mostafa-khalid208/SMART-TECHNOLOGY-APPLICATIONS-IN-AGRICULTURE/APK & Code/smart_irrigation/smart_irrigation/assets/images/8i88iu.jpg

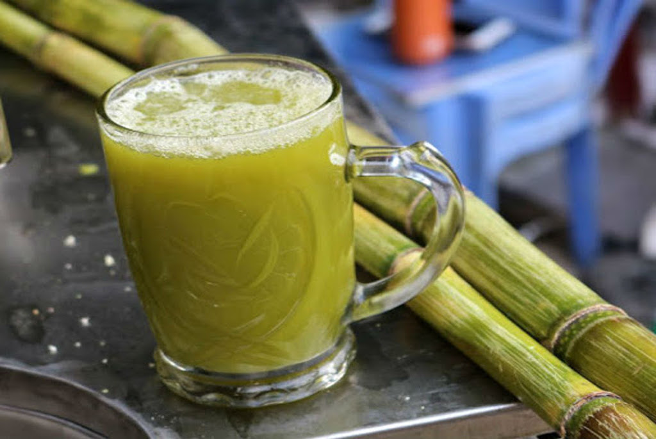
APK & Code/smart_irrigation/smart_irrigation/assets/images/8i88iu.jpg
