mostafa-khalid208/SMART-TECHNOLOGY-APPLICATIONS-IN-AGRICULTURE/APK & Code/smart_irrigation/smart_irrigation/assets/images/2021-10-02.jpg

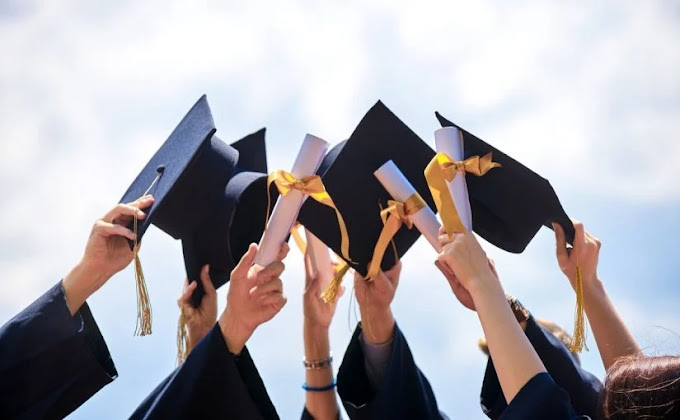
APK & Code/smart_irrigation/smart_irrigation/assets/images/2021-10-02.jpg
