mostafa-khalid208/SMART-TECHNOLOGY-APPLICATIONS-IN-AGRICULTURE/APK & Code/smart_irrigation/smart_irrigation/assets/images/download.jpg

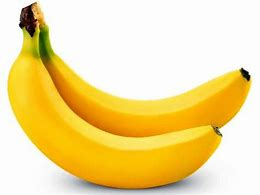
APK & Code/smart_irrigation/smart_irrigation/assets/images/download.jpg
