mostafa-khalid208/SMART-TECHNOLOGY-APPLICATIONS-IN-AGRICULTURE/APK & Code/smart_irrigation/smart_irrigation/assets/images/grg.jpg

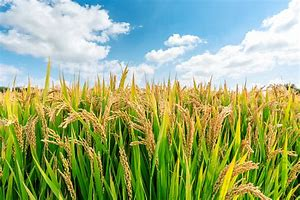
APK & Code/smart_irrigation/smart_irrigation/assets/images/grg.jpg
