mostafa-khalid208/SMART-TECHNOLOGY-APPLICATIONS-IN-AGRICULTURE/Diagram (Fritzing)/Diagram_png.png

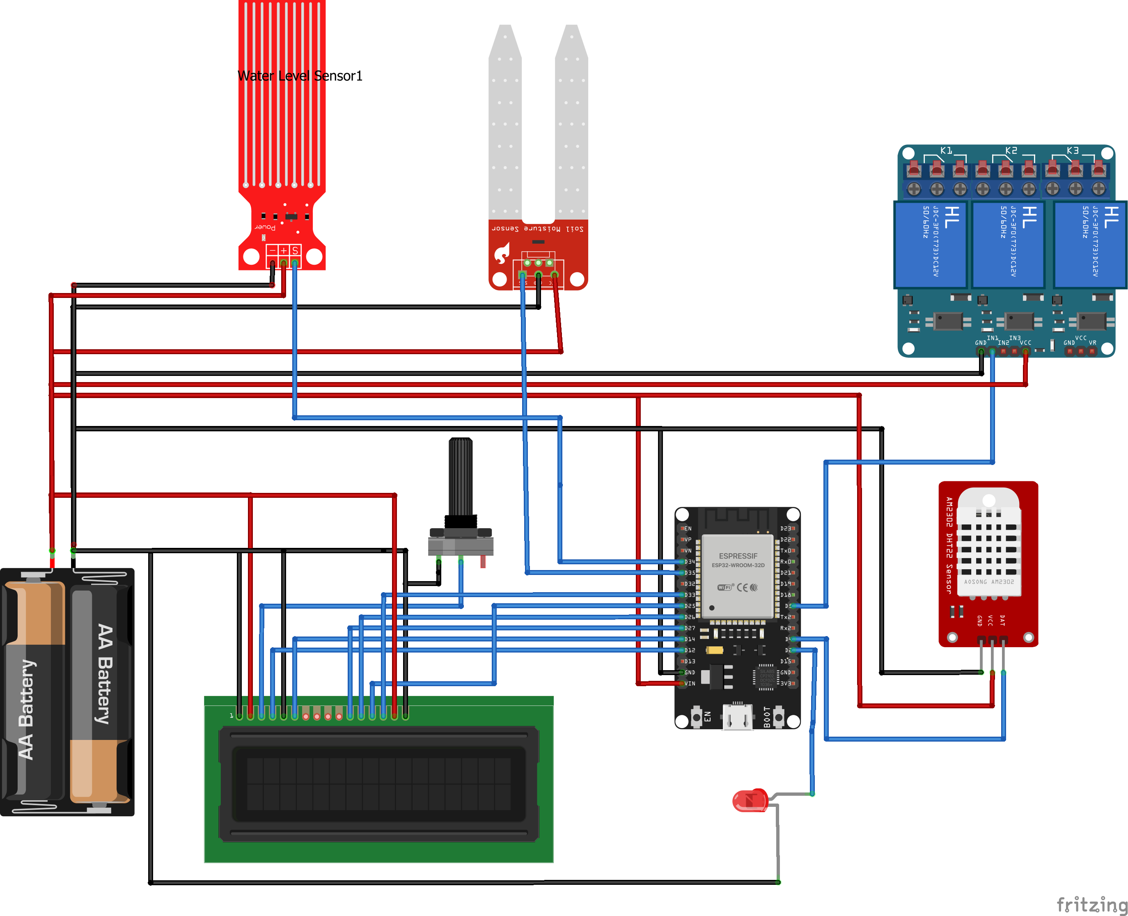
Diagram (Fritzing)/Diagram_png.png
