mostafa-khalid208/SMART-TECHNOLOGY-APPLICATIONS-IN-AGRICULTURE/KiCAD_ESP32/PCB.png

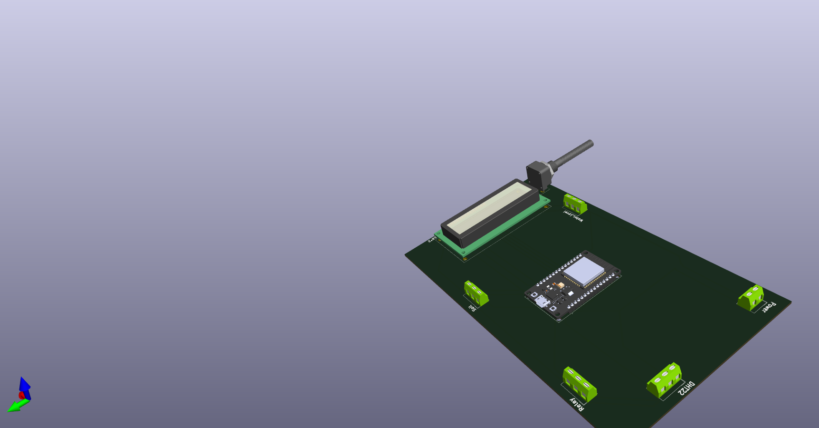
KiCAD_ESP32/PCB.png
