mostafa-khalid208/SMART-TECHNOLOGY-APPLICATIONS-IN-AGRICULTURE/KiCAD_ESP32/PCB_3.jpg

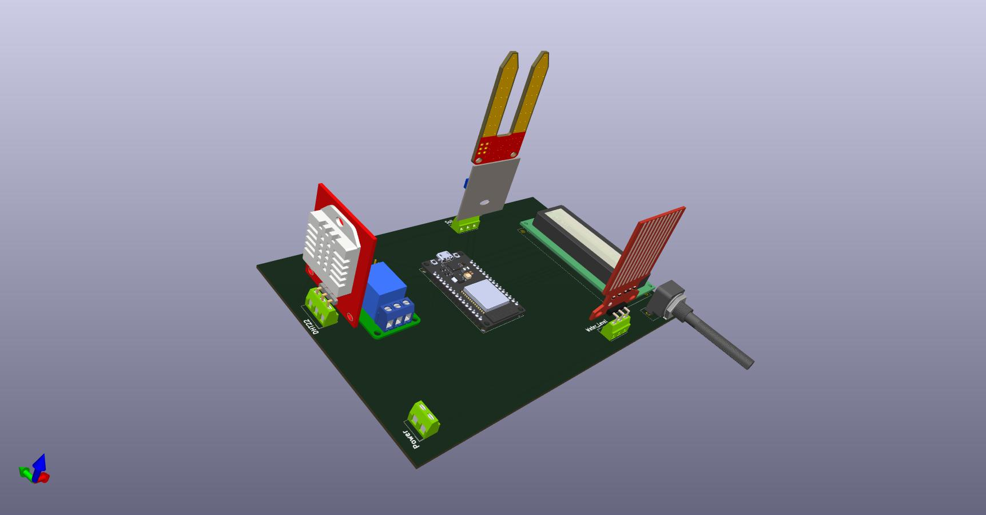
KiCAD_ESP32/PCB_3.jpg
