mostafa-khalid208/SMART-TECHNOLOGY-APPLICATIONS-IN-AGRICULTURE/QRs/All graduation project files (Google Drive).jpg

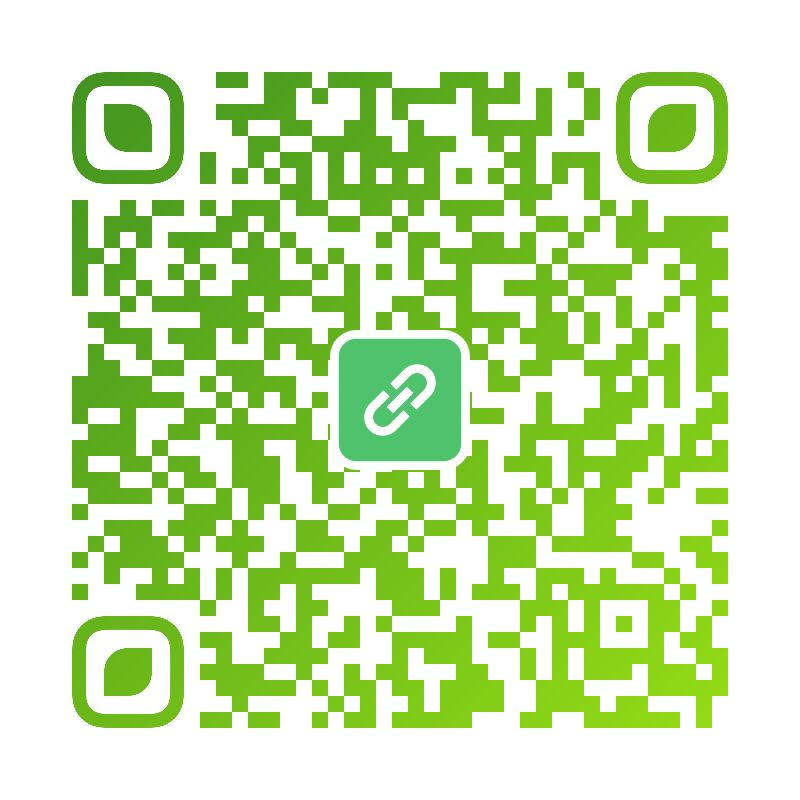
QRs/All graduation project files (Google Drive).jpg
