mostafa-khalid208/SMART-TECHNOLOGY-APPLICATIONS-IN-AGRICULTURE/QRs/Final practical application of the graduation project.jpg

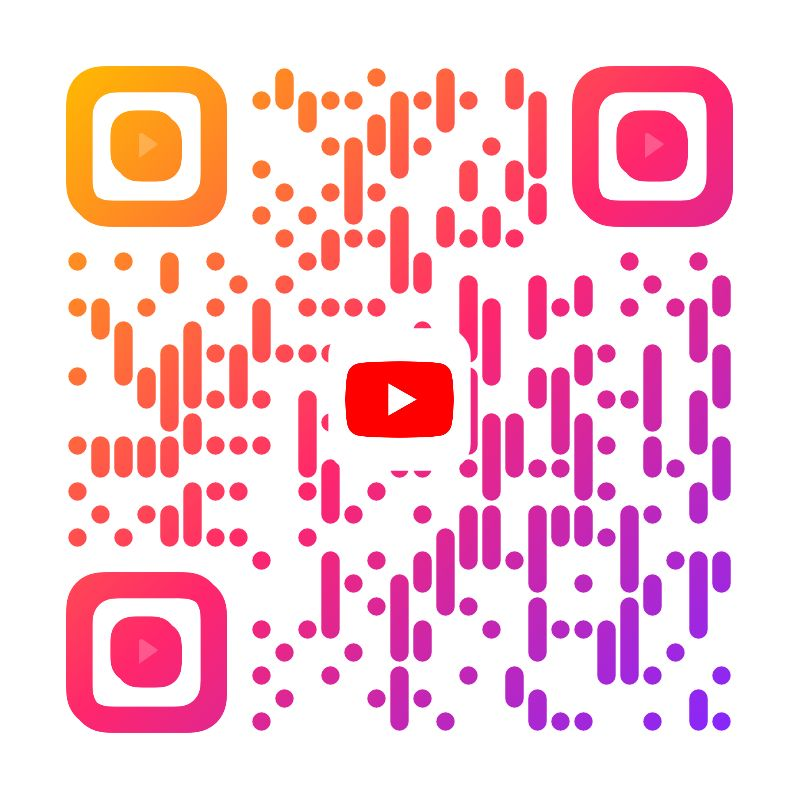
QRs/Final practical application of the graduation project.jpg
