mostafa-khalid208/SMART-TECHNOLOGY-APPLICATIONS-IN-AGRICULTURE/QRs/Github_Link_QR.png

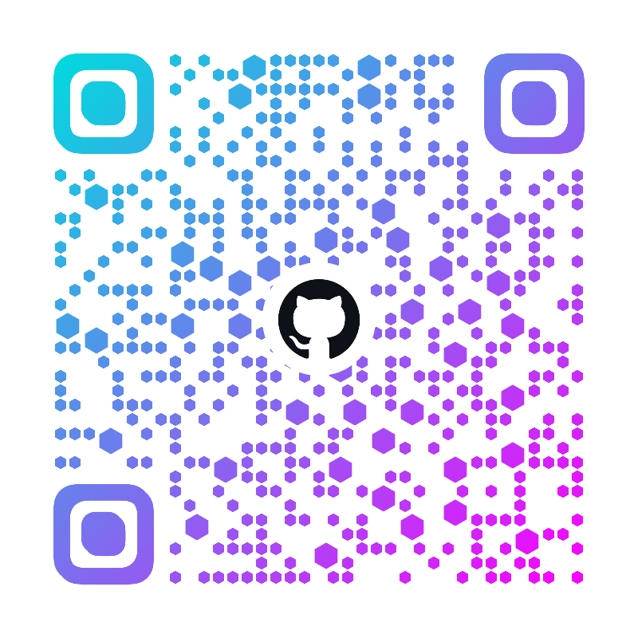
QRs/Github_Link_QR.png
