mostafa-khalid208/SMART-TECHNOLOGY-APPLICATIONS-IN-AGRICULTURE/QRs/Graduation project students with project supervisor.jpg

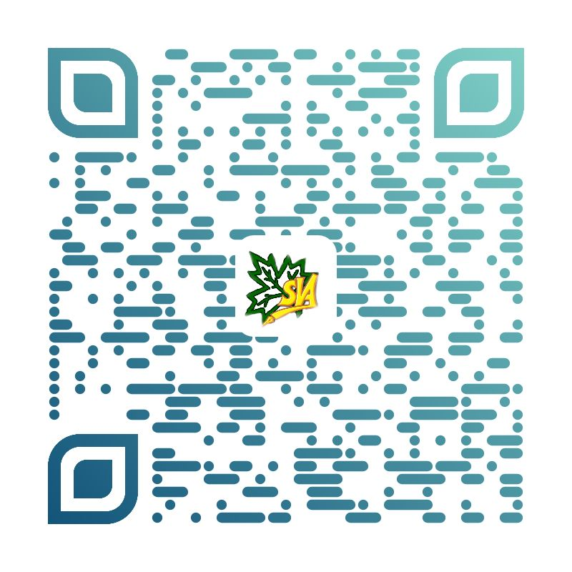
QRs/Graduation project students with project supervisor.jpg
