mostafa-khalid208/SMART-TECHNOLOGY-APPLICATIONS-IN-AGRICULTURE/QRs/Playlist on YouTube has all the videos.png

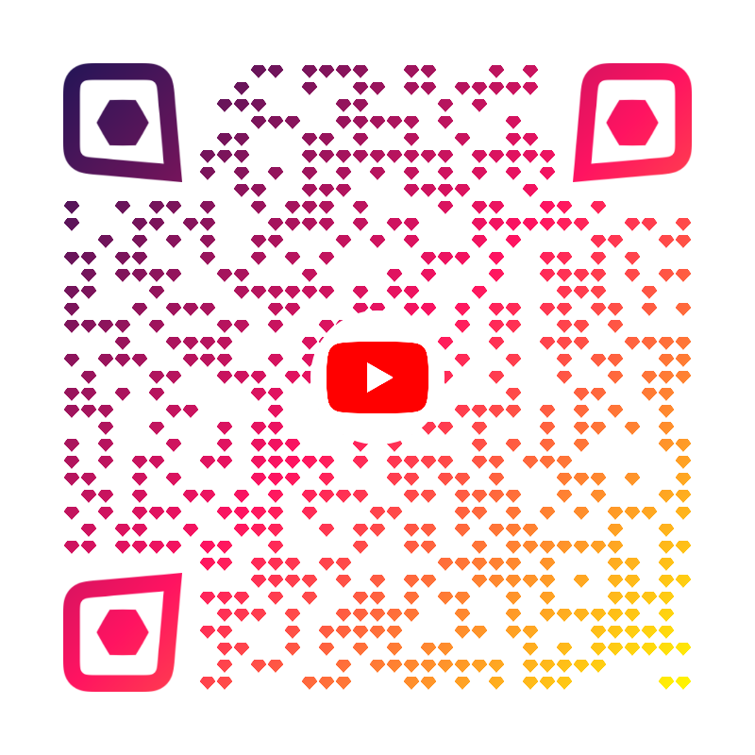
QRs/Playlist on YouTube has all the videos.png
