mostafa-khalid208/SMART-TECHNOLOGY-APPLICATIONS-IN-AGRICULTURE/Students who implemented the project with the project supervisor .jpg

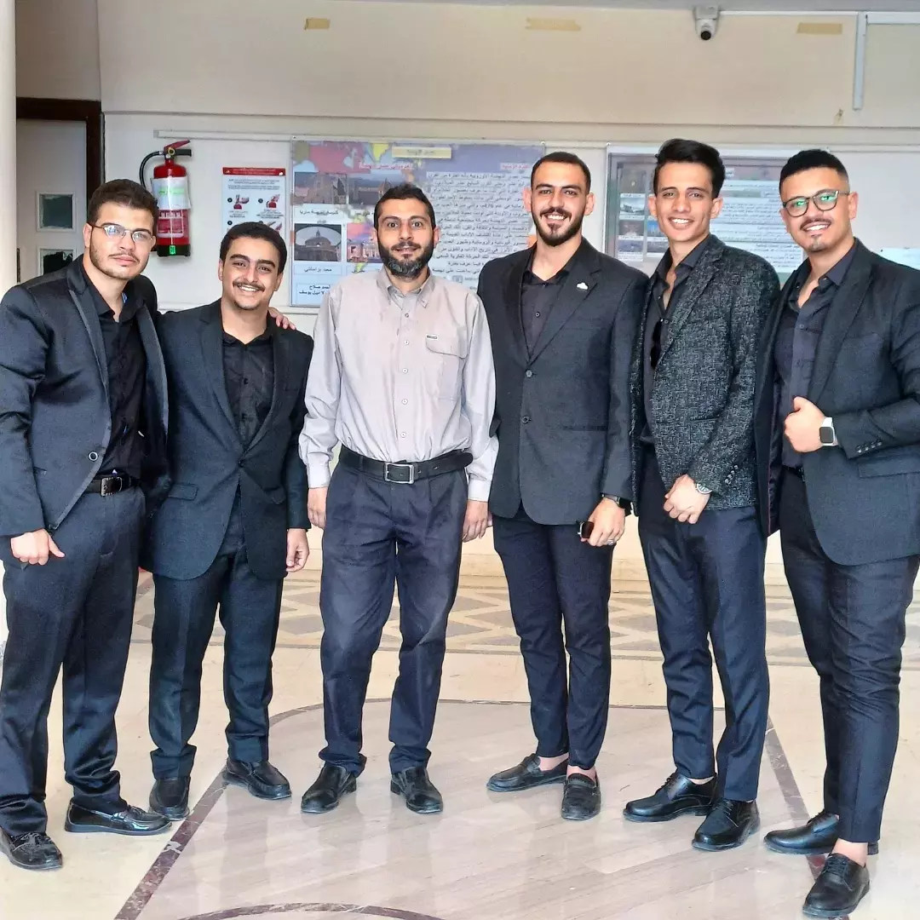
Students who implemented the project with the project supervisor .jpg
