mostafa-khalid208/SMART-TECHNOLOGY-APPLICATIONS-IN-AGRICULTURE/FlowChart.pdf

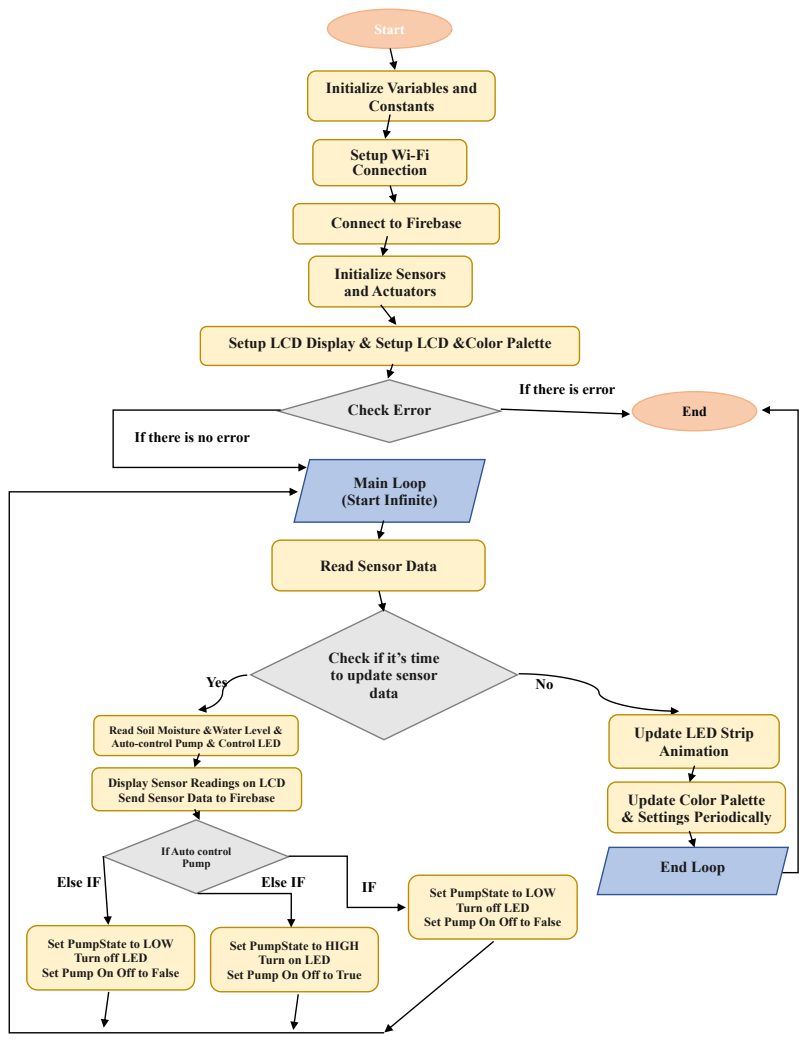
[picture p29: page 1]
Start; Constants; Initialize Sensors and Actuators; Main Loop (Start Infinite); Check Error; End; data; End Loop; Yes; Else IF

Initialize Variables and

Setup Wi-Fi
Connection

Connect to Firebase

Setup LCD Display & Setup LCD &Color Palette

If there is error

If there is no error

Read Sensor Data

Check if it’s time
to update sensor

Read Soil Moisture &Water Level &
Auto-control Pump & Control LED

Update LED Strip
Animation

Display Sensor Readings on LCD
Send Sensor Data to Firebase

Update Color Palette
& Settings Periodically

If Auto control
Pump

Set PumpState to LOW
Turn off LED
Set Pump On Off to False

Set PumpState to HIGH
Turn on LED
Set Pump On Off to True
