mostafa-khalid208/SMART-TECHNOLOGY-APPLICATIONS-IN-AGRICULTURE/Diagram (Fritzing)/Diagram_pdf.pdf

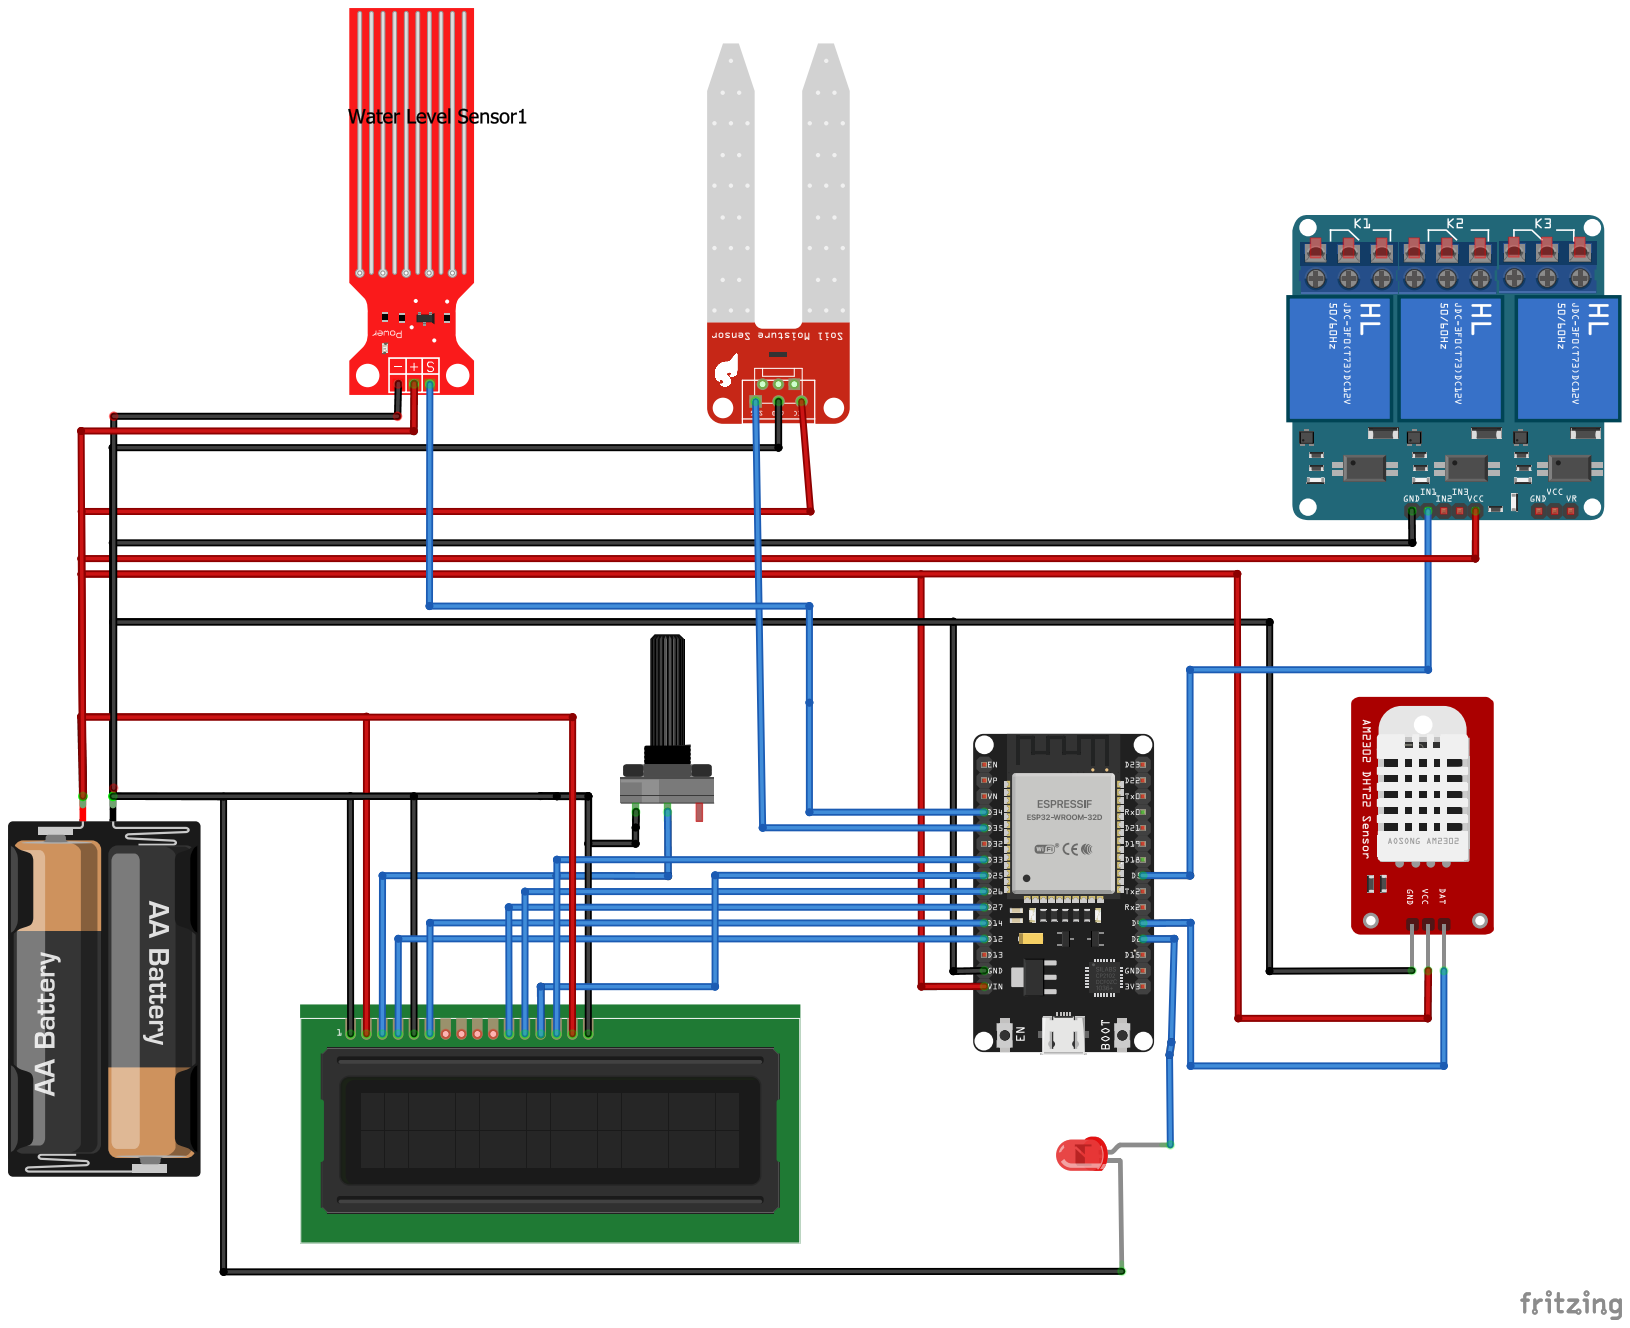
[picture p41: page 1]
